Tinamous/BatteryMonitor/Arduino/Images/AddSigfoxBot.png

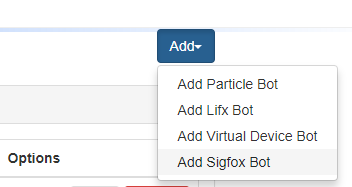
Arduino/Images/AddSigfoxBot.png
