Tinamous/BatteryMonitor/Arduino/Images/AddSigfoxBotDialogBox.png

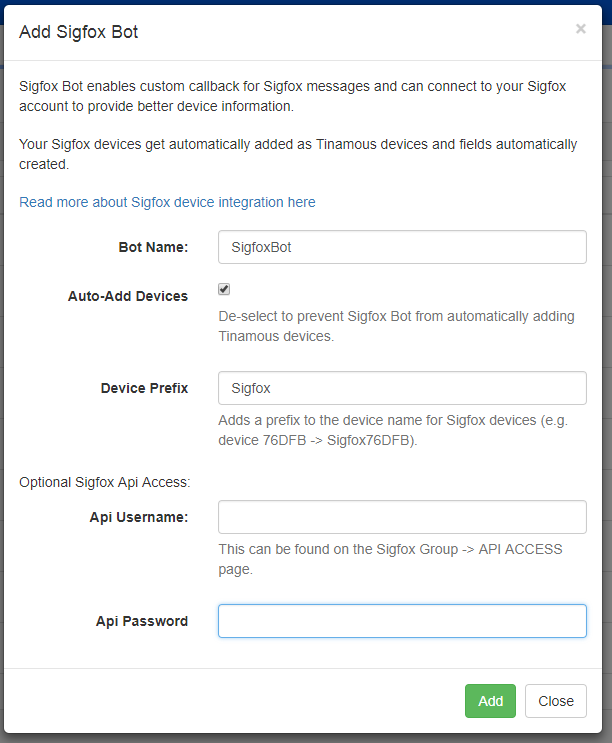
Arduino/Images/AddSigfoxBotDialogBox.png
