Tinamous/BatteryMonitor/Arduino/Images/ApiKeys.png

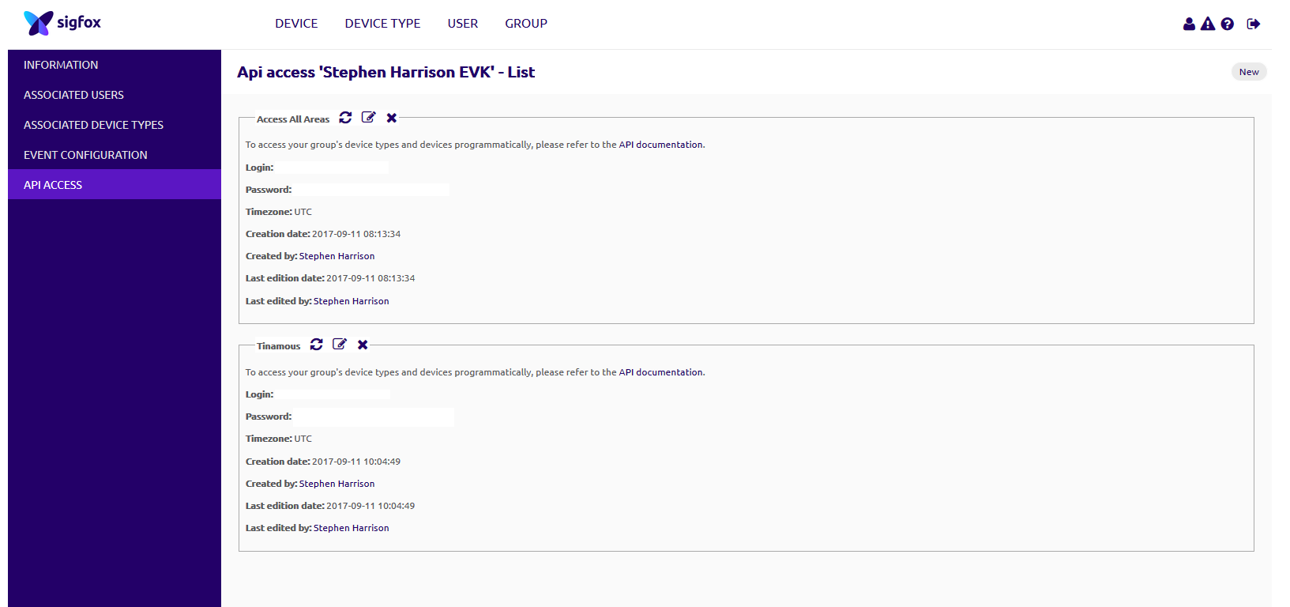
Arduino/Images/ApiKeys.png
