Tinamous/BatteryMonitor/Arduino/Images/CallbackConfig.png

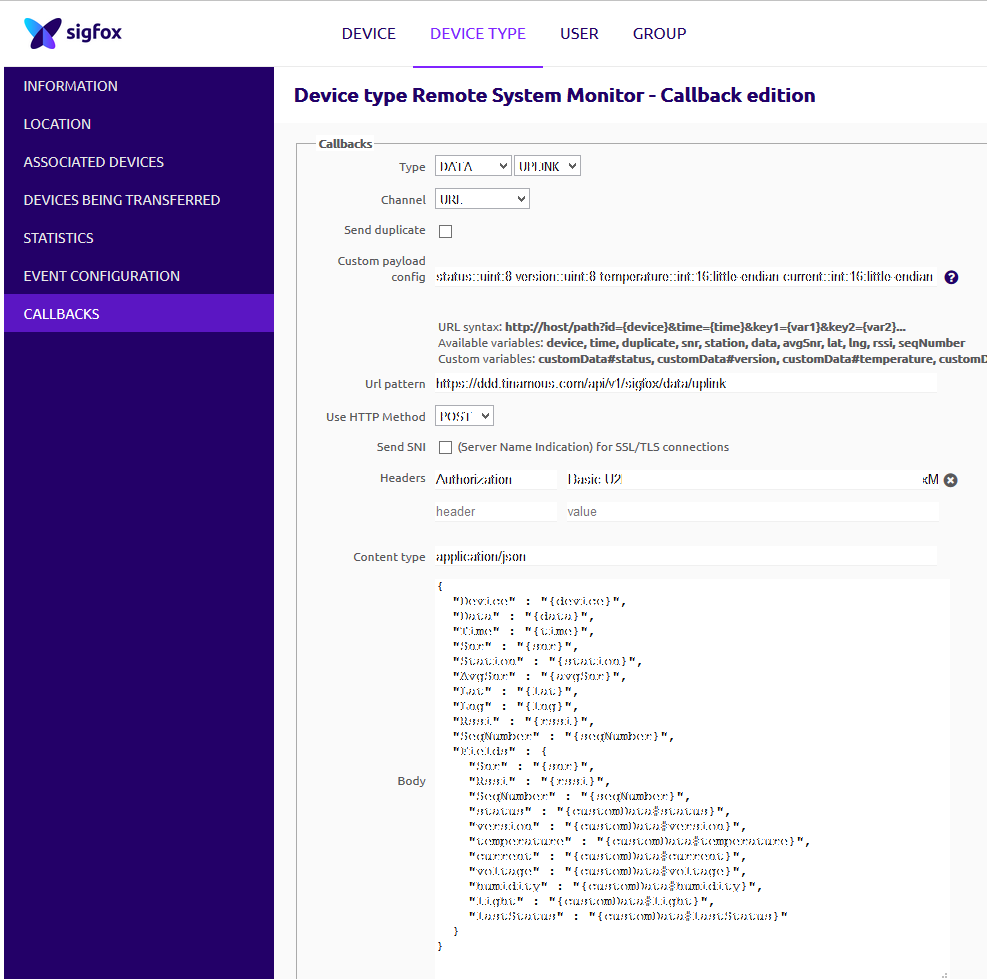
Arduino/Images/CallbackConfig.png
