Tinamous/BatteryMonitor/Arduino/Images/Callbacks.png

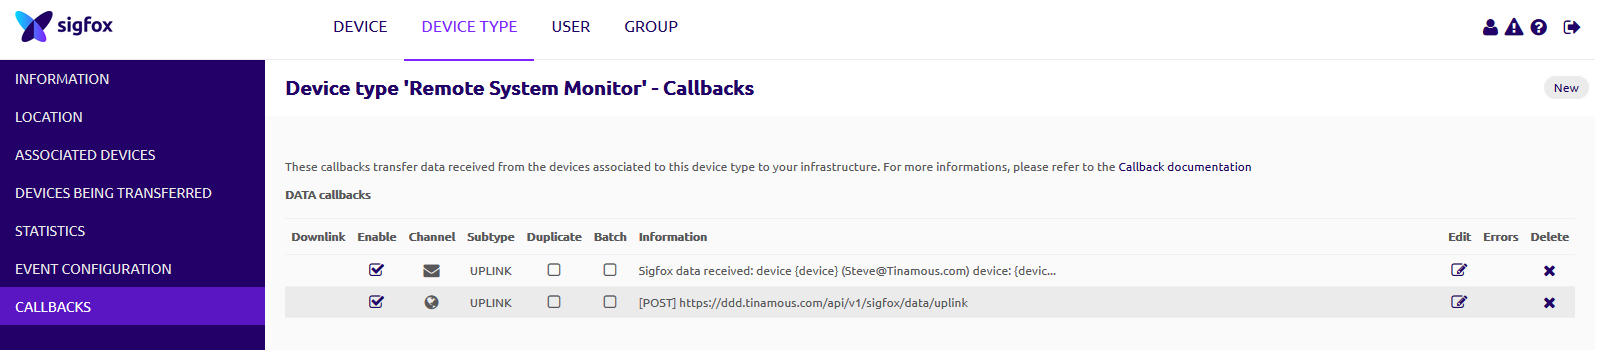
Arduino/Images/Callbacks.png
