Tinamous/BatteryMonitor/Arduino/Images/Dashboard1.png

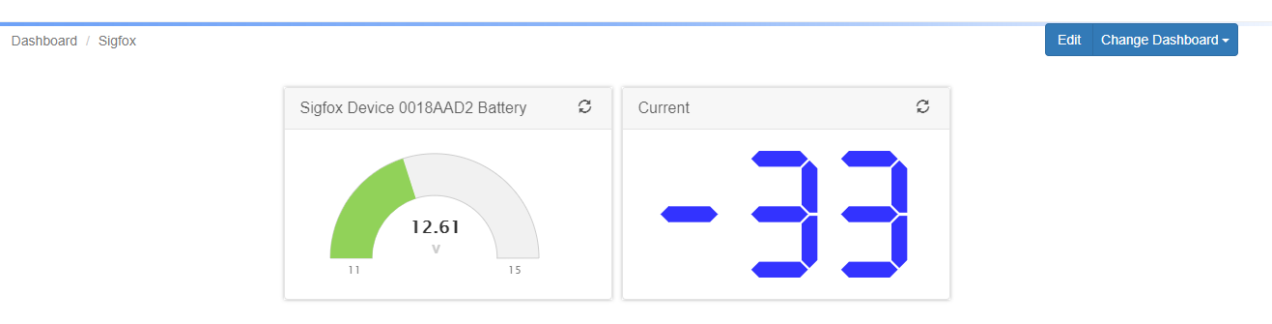
Arduino/Images/Dashboard1.png
