Tinamous/BatteryMonitor/Arduino/Images/DevicePage.png

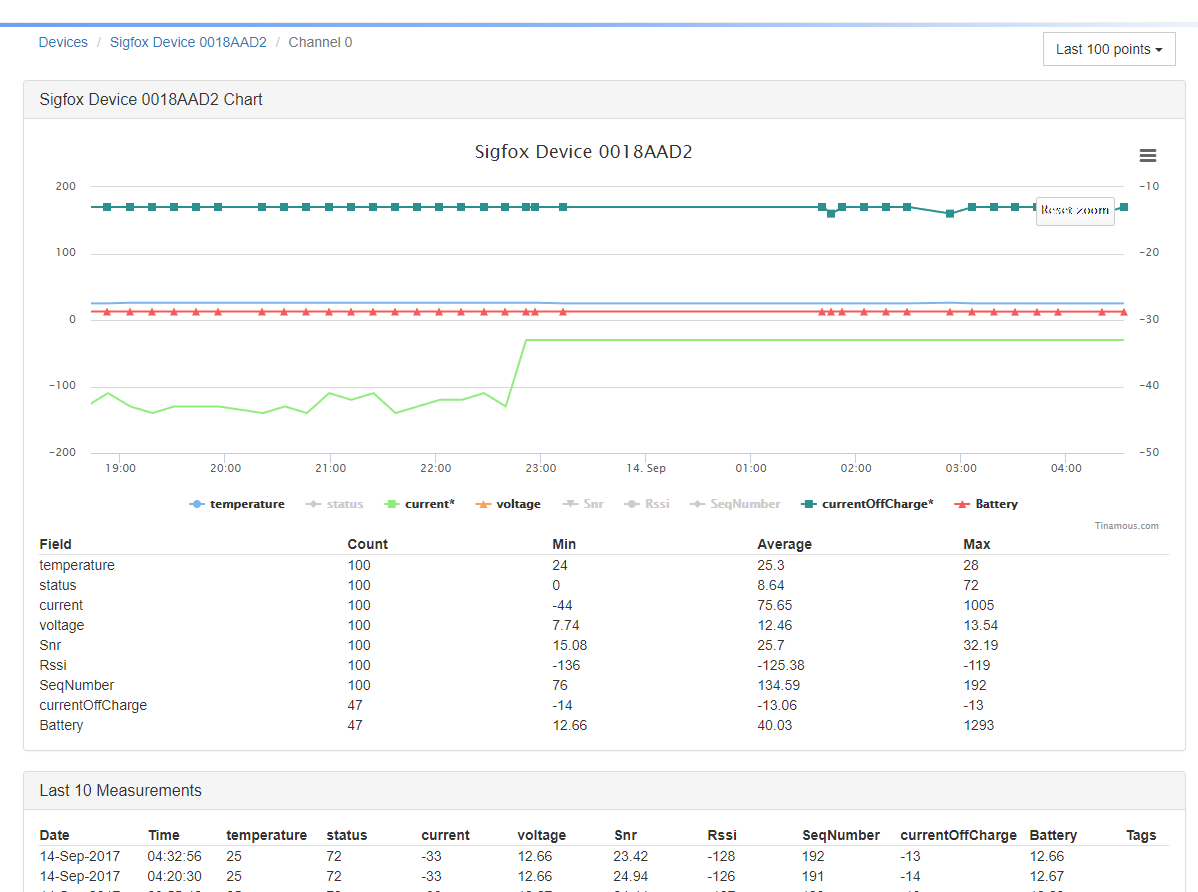
Arduino/Images/DevicePage.png
