Tinamous/BatteryMonitor/Arduino/Images/EditFields.png

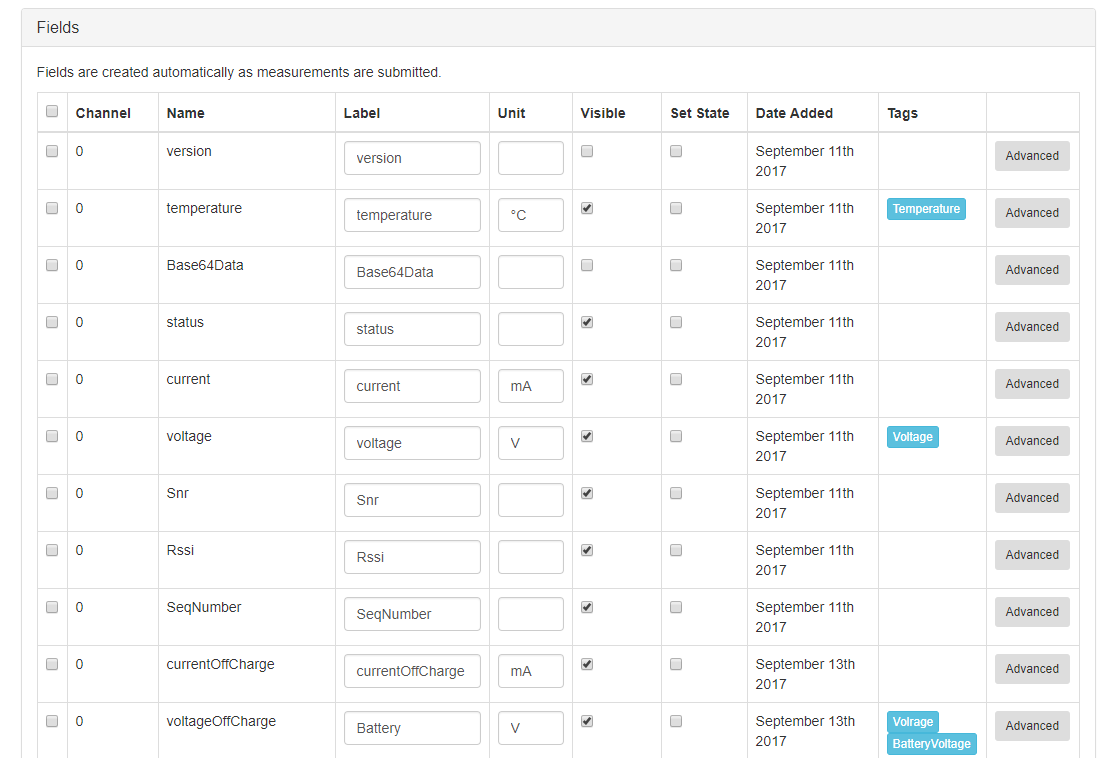
Arduino/Images/EditFields.png
