Tinamous/BatteryMonitor/Arduino/Images/EditVoltageField.png

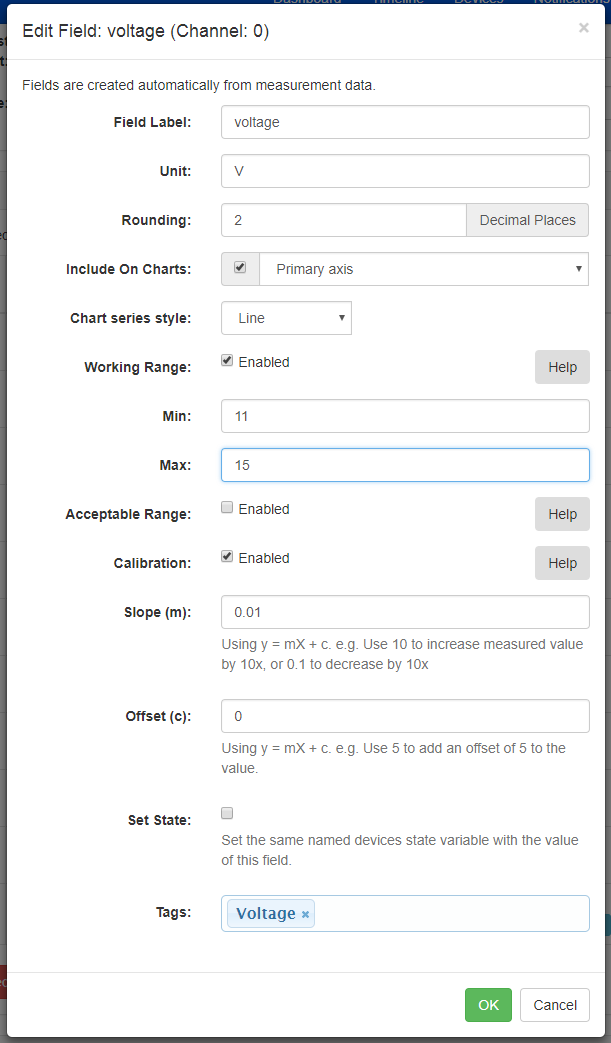
Arduino/Images/EditVoltageField.png
