Tinamous/BatteryMonitor/Arduino/Images/FET.jpg

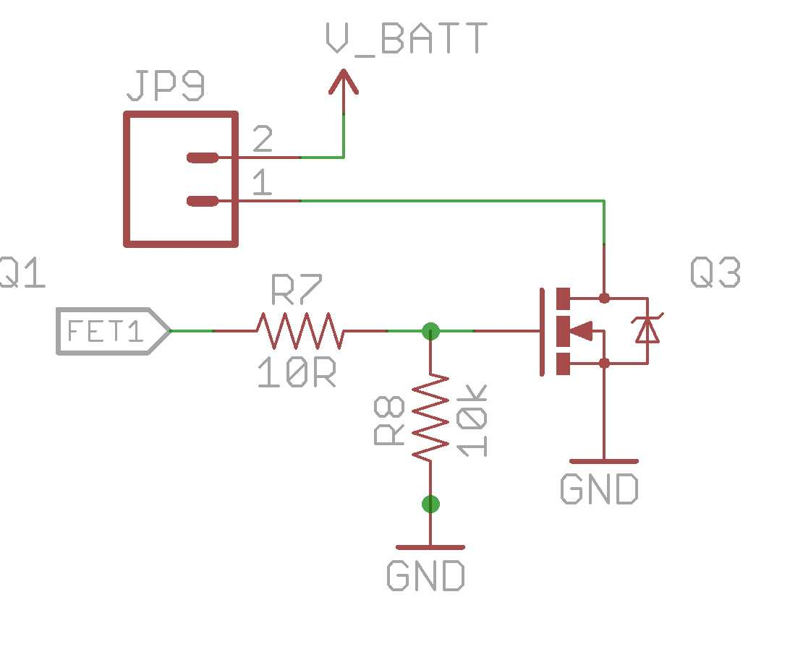
Arduino/Images/FET.jpg
