Tinamous/BatteryMonitor/Arduino/Images/GarageDashboard.jpg

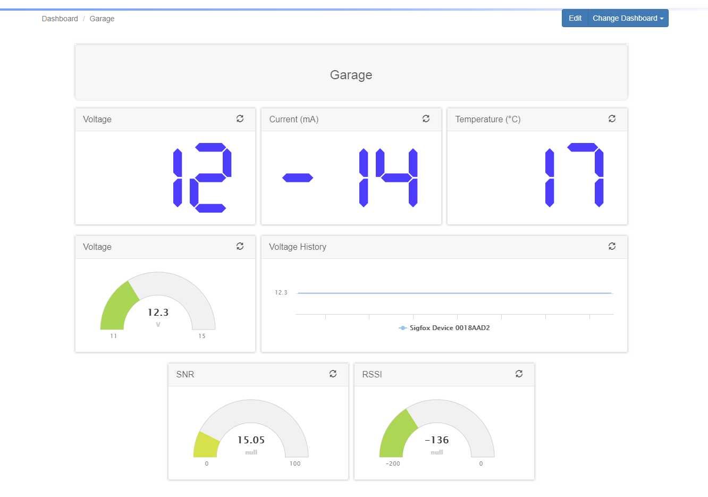
Arduino/Images/GarageDashboard.jpg
