Tinamous/BatteryMonitor/Arduino/Images/LatchingRelay.jpg

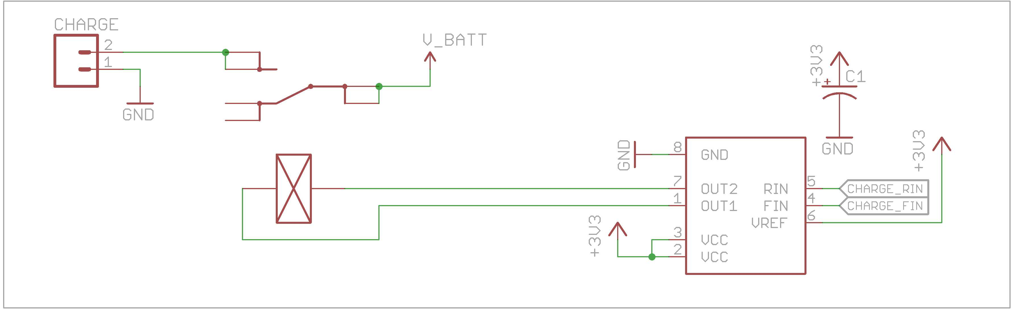
Arduino/Images/LatchingRelay.jpg
