Tinamous/BatteryMonitor/Arduino/Images/Notification1.png

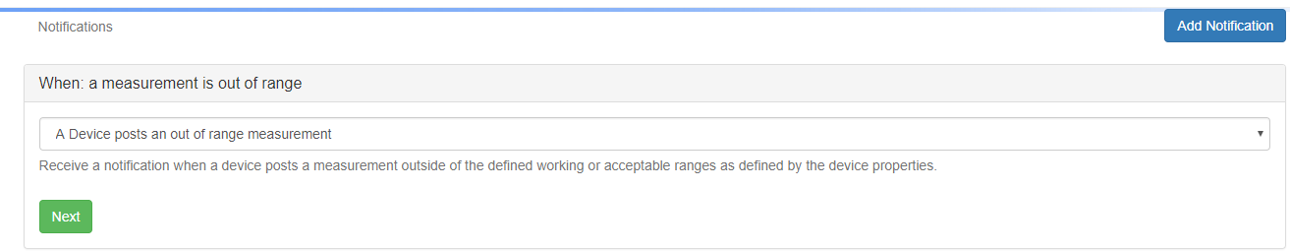
Arduino/Images/Notification1.png
