Tinamous/BatteryMonitor/Arduino/Images/Notification2.png

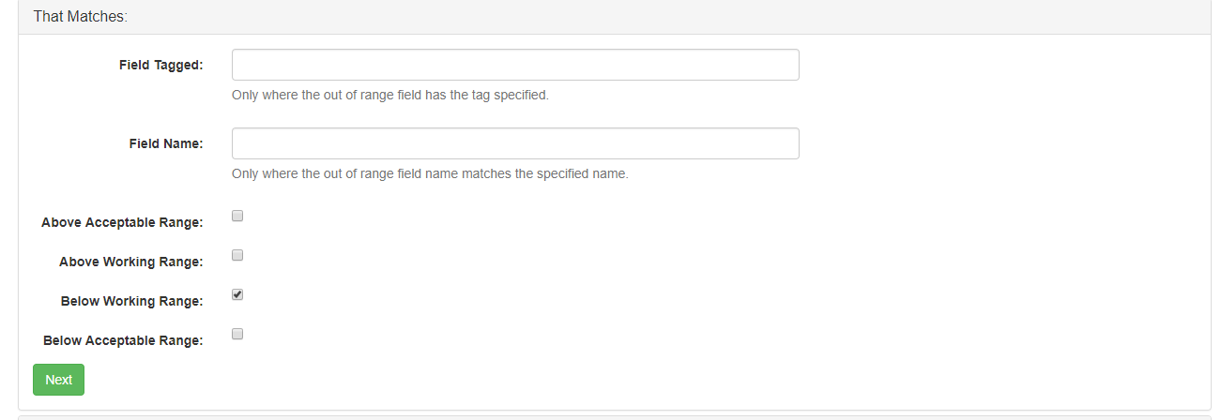
Arduino/Images/Notification2.png
