Tinamous/BatteryMonitor/Arduino/Images/Notification3.png

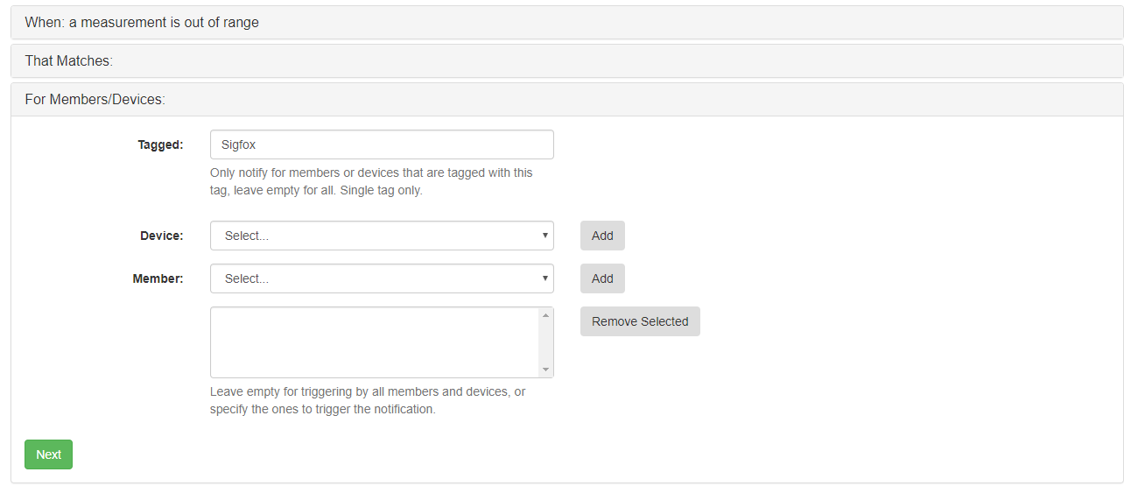
Arduino/Images/Notification3.png
