Tinamous/BatteryMonitor/Arduino/Images/Notification4.png

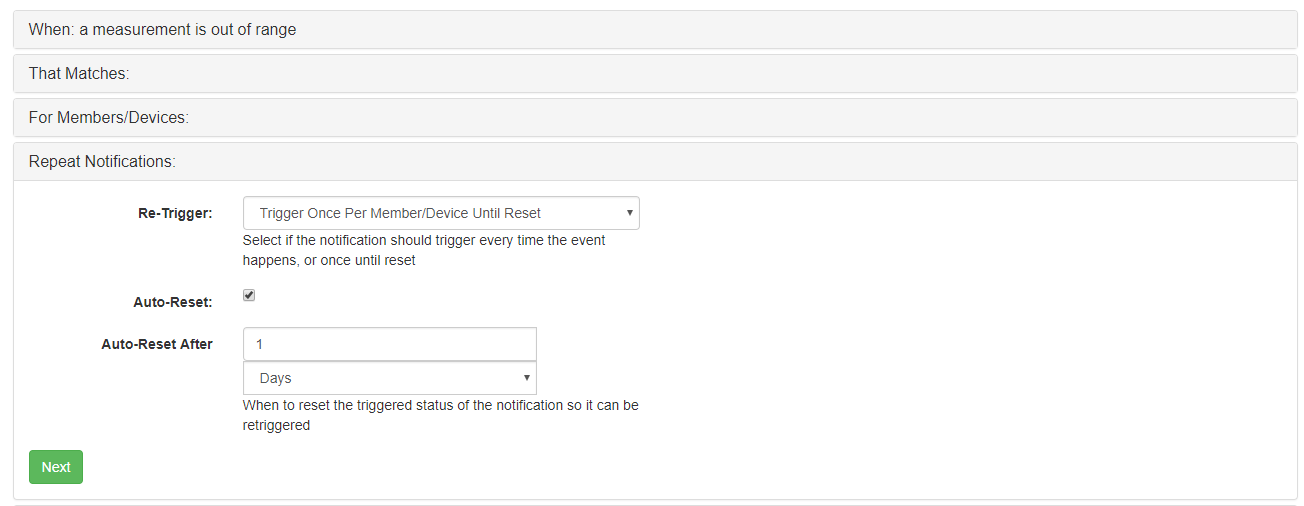
Arduino/Images/Notification4.png
