Tinamous/BatteryMonitor/Arduino/Images/Notification5.png

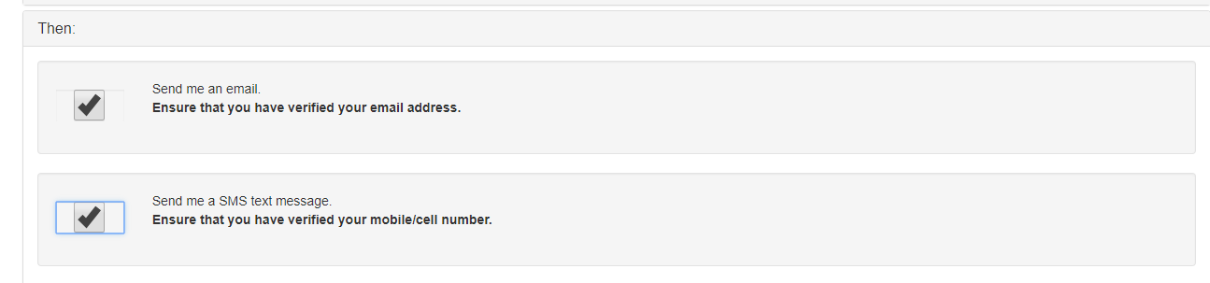
Arduino/Images/Notification5.png
