Tinamous/BatteryMonitor/Arduino/Images/Notification6.png

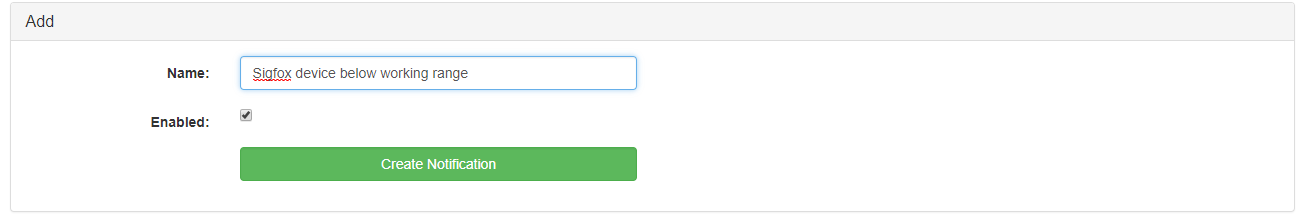
Arduino/Images/Notification6.png
