Tinamous/BatteryMonitor/Arduino/Images/PCBAll.png

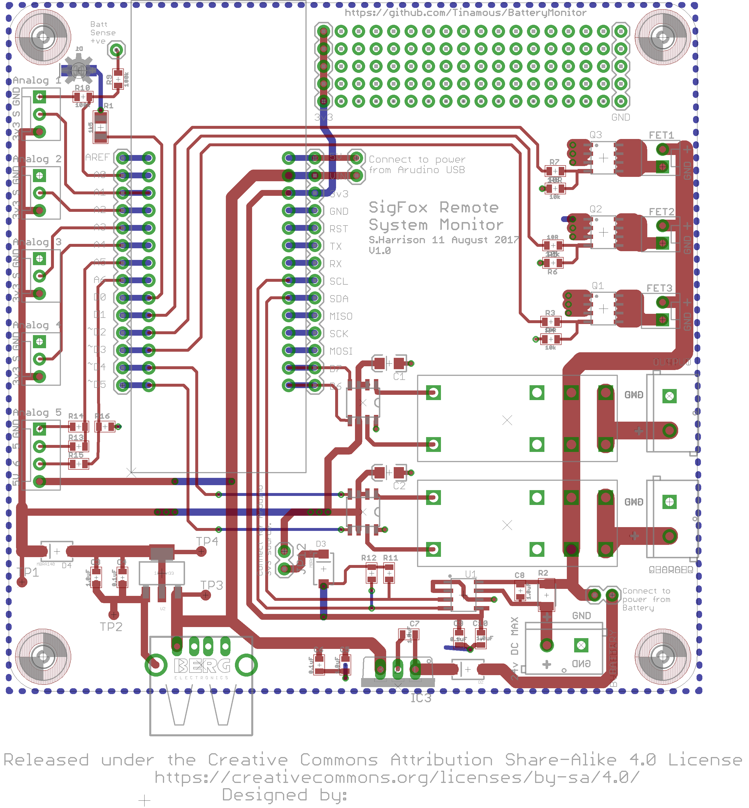
Arduino/Images/PCBAll.png
