Tinamous/BatteryMonitor/Arduino/Images/PcbBottom.png

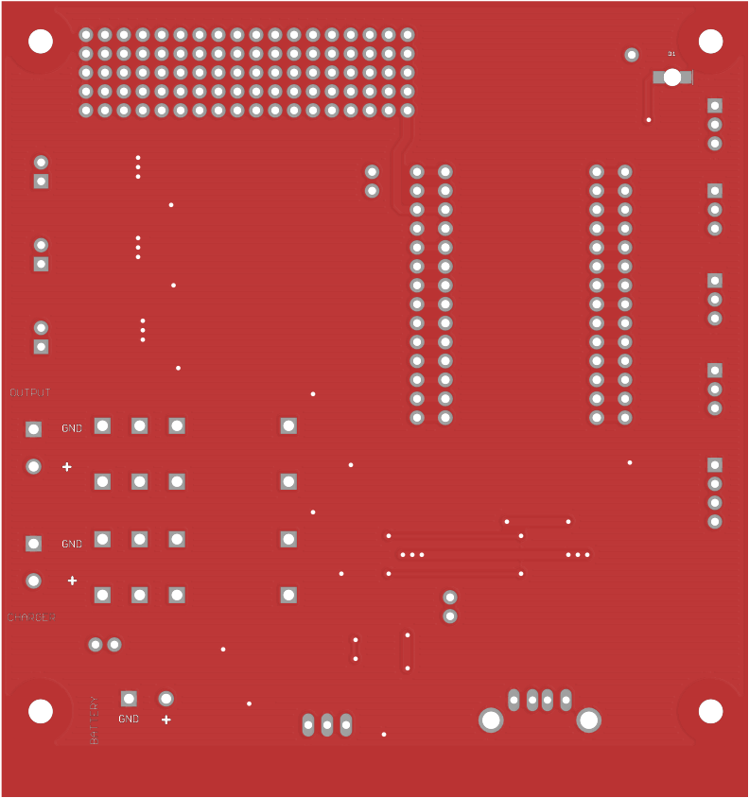
Arduino/Images/PcbBottom.png
