Tinamous/BatteryMonitor/Arduino/Images/PcbEmpty.jpg

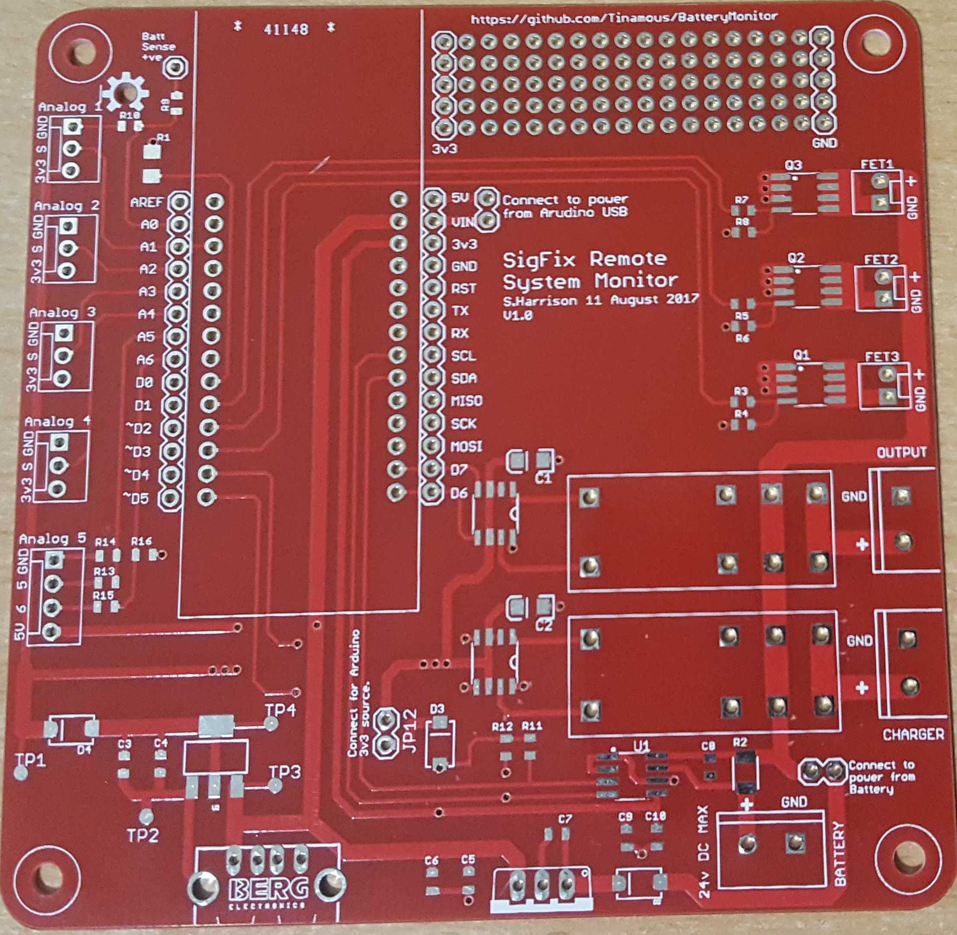
Arduino/Images/PcbEmpty.jpg
