Tinamous/BatteryMonitor/Arduino/Images/PcbTop.png

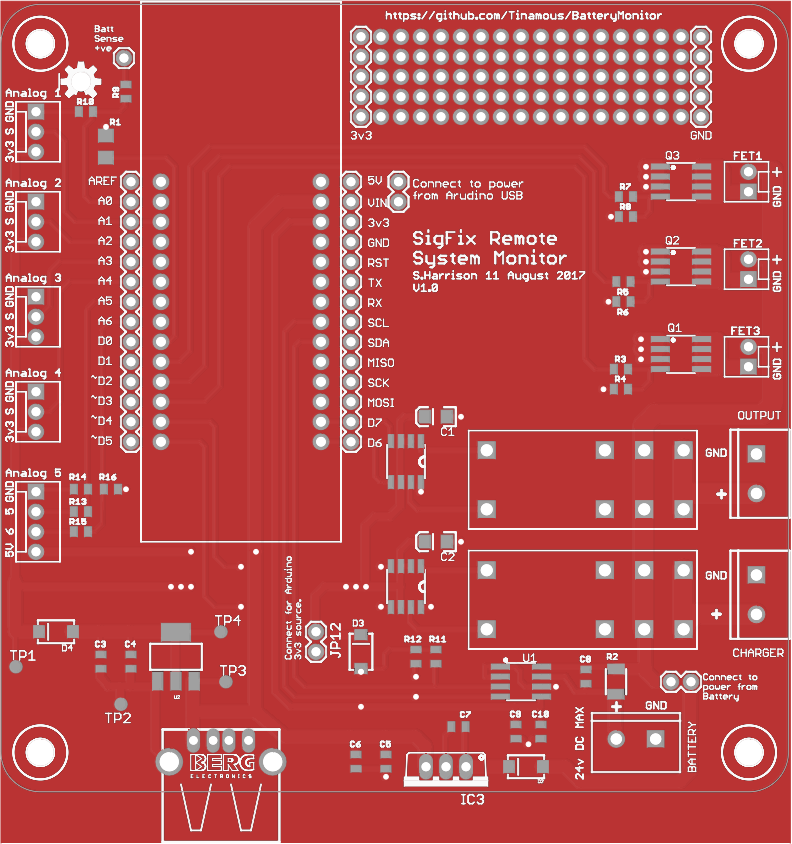
Arduino/Images/PcbTop.png
