Tinamous/BatteryMonitor/Arduino/Images/SigfoxBotCreated.png

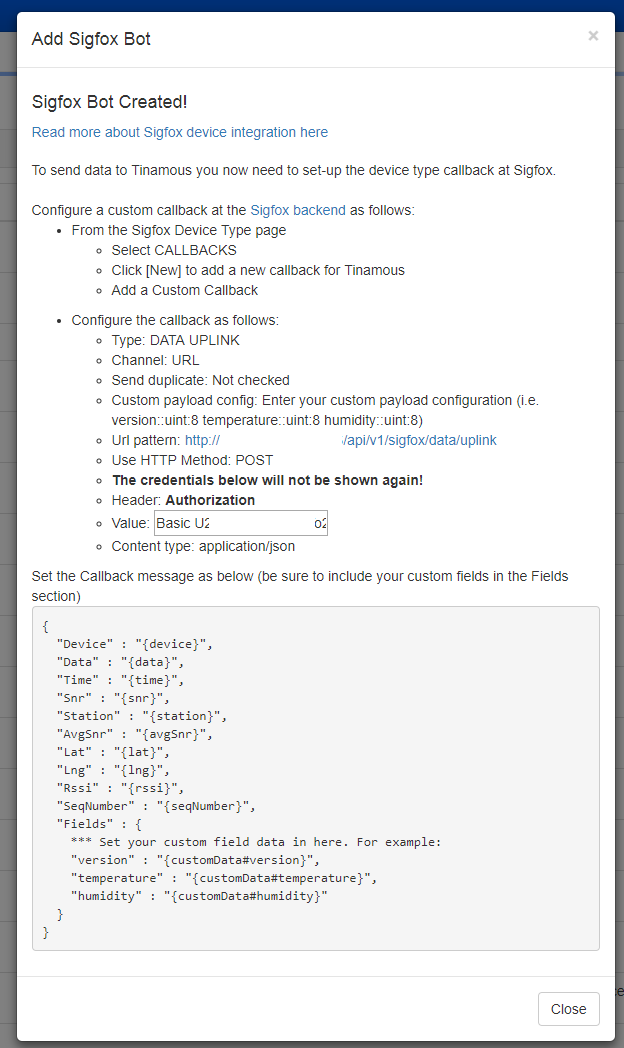
Arduino/Images/SigfoxBotCreated.png
