Tinamous/BatteryMonitor/Arduino/Images/TinamousDeviceList.png

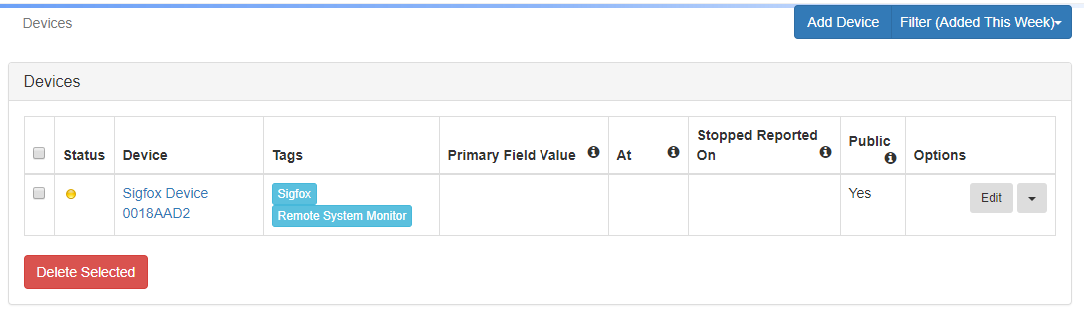
Arduino/Images/TinamousDeviceList.png
