Tinamous/BatteryMonitor/Arduino/Images/TinamousMap.png

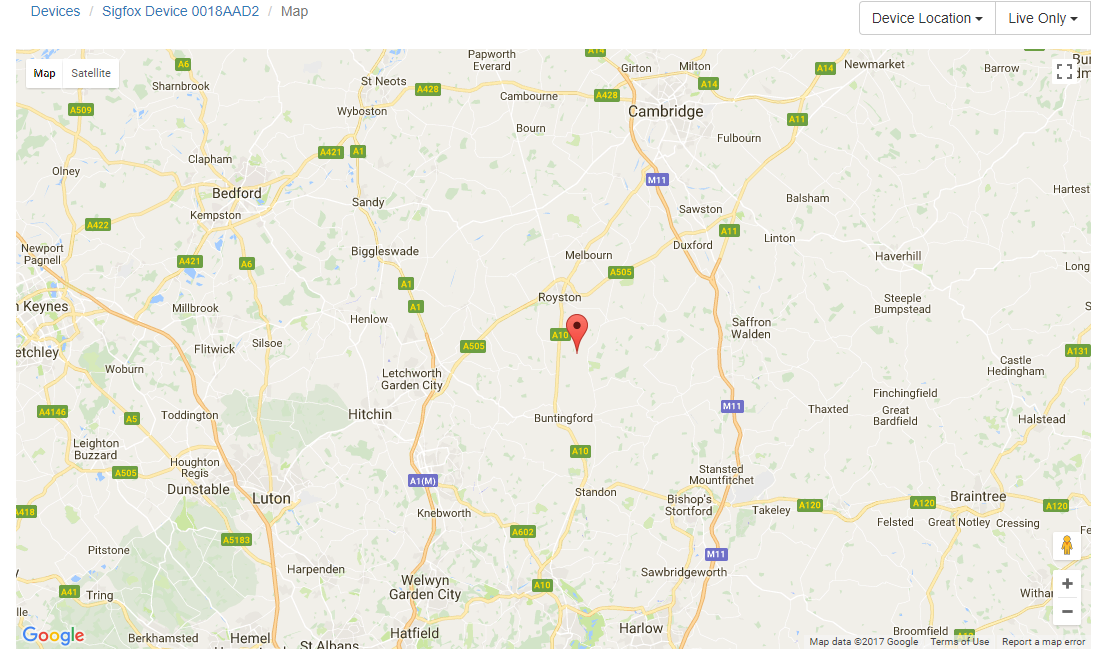
Arduino/Images/TinamousMap.png
