Tinamous/BatteryMonitor/Arduino/Images/Voltage.jpg

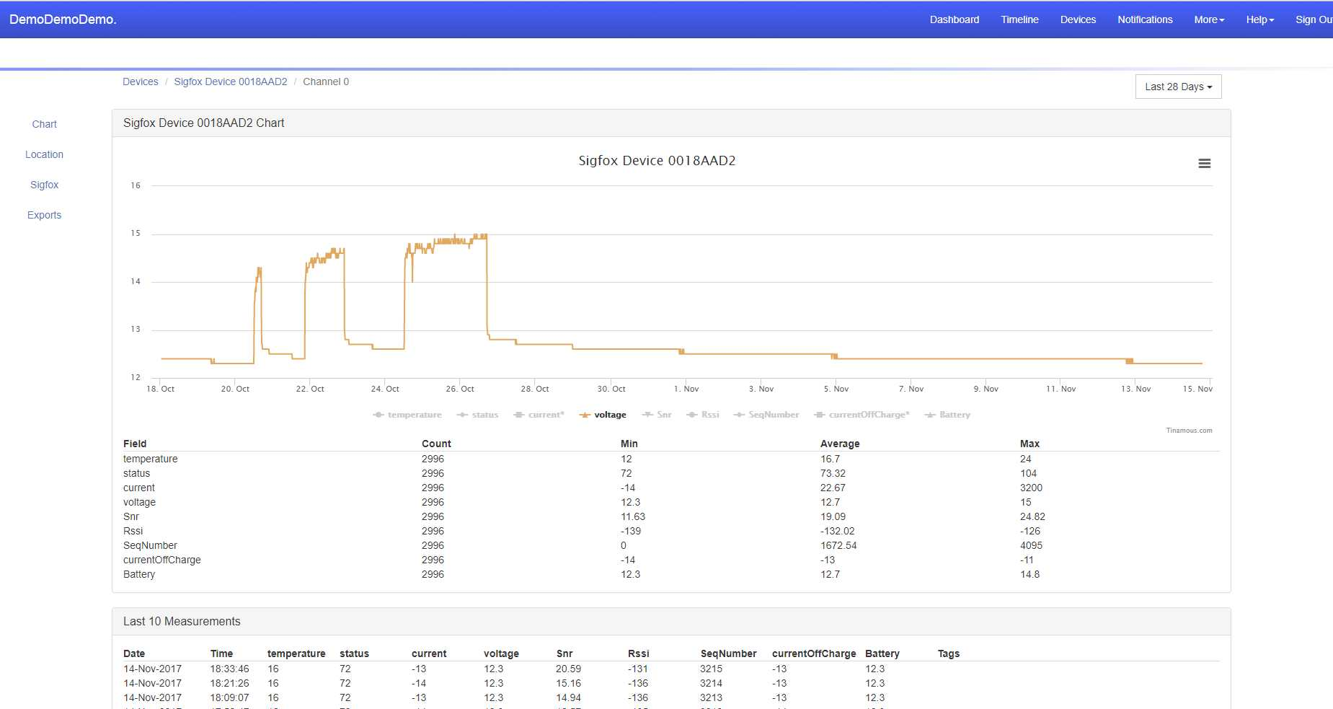
Arduino/Images/Voltage.jpg
